CraigBladow/Heathkit-H8-Enclosure/openscad/H8_side_panels.scad

// Heathkit H8 Computer Enclosure - Side Panels
// Copyright 2024 Craig Bladow
// Released under MIT license:
//          https://github.com/CraigBladow/Heathkit-H8-Enclosure/blob/main/LICENSE

include <H8_parameters.scad>

//Panel Modules
module RoundedEdge(thickness, radius)
{
    rotate([0,0,0])cylinder(h=thickness, r = radius, center = true);
}

module Ledge(L,H,R)
{
    hull()
    {
        translate([0,L/2-R/2,0])cylinder(H,R,R,center=true);
        translate([0,-(L/2-R/2),0])cylinder(H,R,R,center=true);
    }
}

module LidLedge(side)
{
    color("lime")translate([PanelHeight/2-LedgeHeight/2-LedgeRecess,-LedgeOffset,side*(PanelThickness/2+LedgeWidth/2)])rotate([0,0,0]) Ledge(LedgeLength,LedgeWidth,LedgeHeight/2);
}

module FrontPanelLedge(side)
{
    
    color("lime")translate([FP_LedgeOffsetVertical,FP_LedgeOffsetHorizontal,side*(PanelThickness/2+FP_LedgeWidth/2)])
        rotate([0,0,FP_LedgeAngle]) 
            Ledge(FP_LedgeLength,FP_LedgeWidth,FP_LedgeHeight/2);
}

module FrontPanelBracketMount(side)
{
    
    color("lime")translate([FP_LedgeOffsetVertical,FP_LedgeOffsetHorizontal,side*(PanelThickness/2)])

    rotate([0,0,FP_LedgeAngle-90 ]) 
    {
        translate([-FPB_LengthLongShift,-FPB_LengthShortWidth/2+0.2,0])FrontPCB_Bracket();//0.2 is a magic tweak
    }
}

module FrontPanelBracketMountInsets(side)
{
    
    translate([FP_LedgeOffsetVertical,FP_LedgeOffsetHorizontal,side*(PanelThickness/2-Insert_6_32_hole_depth/2)])
        rotate([0,0,FP_LedgeAngle-90 ]) 
    {
             translate([-FPB_LengthLongShift-FPB_LengthLong/2 +(FPB_HoleDiameter*1.75)- FPB_MountShift,-FPB_LengthShortWidth/2+0.2,0])     translate([0,0,0]) rotate([0,0,180]) Insert_IUB_632_2(); 
                          translate([-(FPB_LengthLongShift-FPB_LengthLong/2 +(FPB_HoleDiameter*1.75)- FPB_MountShift)-FPB_UpperHoleShift,-FPB_LengthShortWidth/2+0.2,0])     translate([0,0,0]) rotate([0,0,180]) Insert_IUB_632_2(); 
    }
    
}

module OrigPanel()  // todo delete
{
    hull()
    {
        translate([PanelHeight/2-PanelCornerRadius,-PanelOverallLength/2+PanelCornerRadius,0])RoundedEdge(PanelThickness,PanelCornerRadius);  // upper rear corner
        translate([-PanelHeight/2+PanelCornerRadius,-PanelOverallLength/2+PanelCornerRadius,0])RoundedEdge(PanelThickness,PanelCornerRadius);  // lower rear corner

        
        translate([-PanelHeight/2+PanelCornerRadius+PanelFrontBottomRecessHeight,PanelOverallLength/2-PanelCornerRadius,0])RoundedEdge(PanelThickness,PanelCornerRadius);  // lower front corner (not bottom)
        translate([-PanelHeight/2+PanelCornerRadius,PanelOverallLength/2-PanelCornerRadius-PanelFrontBottomRecessLength,0])RoundedEdge(PanelThickness,PanelCornerRadius);  // bottom front corner (recessed)
        translate([PanelHeight/2-PanelCornerRadius,PanelTopLength-PanelOverallLength/2-PanelCornerRadius,0])RoundedEdge(PanelThickness,PanelCornerRadius);  // upper front corner

    }
}

module Panel()
{
    R = PanelCornerRadius;
    D = R * 2;
    PH = PanelHeight/2 - R;
    POL = PanelOverallLength/2 - R;
    linear_extrude(PanelThickness, center = true)
        offset(r = PanelCornerRadius)
            polygon([ [PH,-POL],
                      [-PH,-POL],        
                      [-PH,POL - PanelFrontBottomRecessLength],
                      [-PH+PanelFrontBottomRecessHeight,POL],
                      [PH,PanelTopLength-PanelOverallLength/2]]);   
}


module BackPanelBoltHoles()
{
    BoltClearanceY_Offset = 0;
    BoltClearanceX_Offset1 = BackPanelMountLength/2 -WasherRecessDiameterTopNo8;
    BoltClearanceX_Offset2 = -BoltClearanceX_Offset1;
    BoltClearanceZ_Offset = -(BackPanelThickness+BaseMountThickness+0)/2+WasherEmbossDepth;

    color("Magenta")translate([BoltClearanceX_Offset1,BoltClearanceY_Offset,BoltClearanceZ_Offset])rotate([180,0,0])BoltWasherHoleNo8();
    color("Magenta")translate([BoltClearanceX_Offset2,BoltClearanceY_Offset,BoltClearanceZ_Offset])rotate([180,0,0])BoltWasherHoleNo8();
}

module BackPanelRails()
{ 
    difference(){
       // Back panel mounting rails

        translate([-BackPanelRailsOffset,-PanelOverallLength/2+BasePlateHeight/2+BackPanelRecess,PanelThickness/2+BaseMountLength/2])rotate([90,0,0])
       difference(){ 
            PanelMount(BackPanelMountLength);
            BackPanelBoltHoles();
        }
       // remove excess fillet on bottom    
       translate([0,-PanelOverallLength/2-PanelThickness*2,0])cube([PanelHeight,PanelThickness*4,PanelThickness*4],center=true);
    }

}

BasePlateMountingRailsOffset = -(PanelOverallLength-BaseMountWidth)/2 +(BackPanelRecess+BackSupportThickness);
//echo(BasePlateMountingRailsOffset = BasePlateMountingRailsOffset);
   
module BasePlateMountingRailBoltHoles()
{
    BoltClearanceX_Offset = -PanelHeight/2+BasePlateRecess+BasePlateHeight+BaseMountThickness/2-WasherEmbossDepth;
    BoltClearanceY_Offset1 = -WasherRecessDiameterTopNo8;
    BoltClearanceY_Offset2 = -BoltClearanceY_Offset1;
    BoltClearanceY_Offset3 = BaseMountWidth/2-WasherRecessDiameterTopNo8 + BasePlateMountingRailsOffset;
    BoltClearanceY_Offset4 = -BaseMountWidth/2 + WasherRecessDiameterTopNo8 + BasePlateMountingRailsOffset;//-BoltClearanceY_Offset3;
    
    color("Magenta")translate([BoltClearanceX_Offset,BoltClearanceY_Offset1,PanelThickness/2+BaseMountLength/2])rotate([0,90,0])BoltWasherHoleNo8();
    color("Magenta")translate([BoltClearanceX_Offset,BoltClearanceY_Offset2,PanelThickness/2+BaseMountLength/2])rotate([0,90,0])BoltWasherHoleNo8();
    color("Magenta")translate([BoltClearanceX_Offset,BoltClearanceY_Offset3,PanelThickness/2+BaseMountLength/2])rotate([0,90,0])BoltWasherHoleNo8();
    color("Magenta")translate([BoltClearanceX_Offset,BoltClearanceY_Offset4,PanelThickness/2+BaseMountLength/2])rotate([0,90,0])BoltWasherHoleNo8();    
    
}


module BasePlateMountingRails()
{

    difference(){   
            
        translate([-PanelHeight/2+BasePlateHeight/2+BasePlateRecess,BasePlateMountingRailsOffset,PanelThickness/2+BaseMountLength/2])rotate([90,0,90]) PanelMount(BaseMountWidth);

        // remove excess fillet on bottom    
        translate([-PanelHeight/2-PanelThickness*2,0,0])color("lime")cube([PanelThickness*4,PanelOverallLength,PanelThickness*4],center=true);
        
       BasePlateMountingRailBoltHoles(); 
                        
    }
}

module PCB_InsertMountPoints()
{
    Insert_IUB_632_2();
}


module LeftPanel()
{
    difference()
    {
        union()
        {
            Panel();
            LidLedge(left);
            FrontPanelLedge(left);
            BackPanelRails();
            BasePlateMountingRails();
            
        }
        SidePlaneMountingInsets();
        FrontPanelBracketMountInsets(left); 
        SidePlaneFrontPanelMountingInset();
        
    }
    
}


module PanelMount(PM_Width)
{
        translate([0,0,BasePlateHeight/2])BaseMount(PM_Width);
        translate([0,0,-BasePlateHeight/2])rotate([180,0,180])BaseMount(PM_Width);
}

module FrontLeftPanel()
{
    difference()
    {

        LeftPanel();
        
        // Leave a small gap so printed half panels fit together easily
        TheGap(PanelHeight * 2,Gap,PanelThickness * 8);
        
        // Remove other half of left panel
        translate([0,-PanelOverallLength/2,0]) cube([PanelHeight*2,PanelOverallLength,PanelThickness * 4],center=true);
        // Make Sockets for pins
        SidePinPlugSockets(PanelHeight);
    }
}


module TheGap(G_X,G_Y,G_T)
{
    union()
    {
        //cube([G_X,G_Y,G_T],center = true);
        BML = BaseMountLength+0.1;
        color("red") translate([0,0,-(-PanelThickness/2+ridge_h/2-BML/2)])cube([PanelHeight,2*ridge_w+Gap,ridge_h+BML],center=true);
    }
    
}


module RearLeftPanel()
{
    difference()
    {
        LeftPanel();
        TheGap(PanelHeight * 2,Gap,PanelThickness * 8);    
        // Remove other half of left panel
        translate([0,PanelOverallLength/2,0]) cube([PanelHeight*2,PanelOverallLength,PanelThickness * 4],center=true);
        // Make sockets for pins
        SidePinPlugSockets(PanelHeight);
    }
}

module RightPanel()
{
    rotate([180,0,0])mirror([0,1,0])LeftPanel();
}

module FrontRightPanel()
{
    rotate([180,0,0])mirror([0,1,0]) FrontLeftPanel();
}

module RearRightPanel()
{
    rotate([180,0,0])mirror([0,1,0]) RearLeftPanel();
}



module Insert_IUB_632_2()
{
    union()
    {
        translate([0,0,Insert_6_32_taper_length/2])cylinder(h = Insert_6_32_taper_length, r1 = Insert_6_32_bottom_dia/2,r2 = Insert_6_32_opening_dia/2, center = true); 
        translate([0,0,-(Insert_6_32_hole_depth - Insert_6_32_taper_length)/2])cylinder(h = (Insert_6_32_hole_depth - Insert_6_32_taper_length), r = Insert_6_32_bottom_dia/2, center = true);
        
    }
}


module SidePinSnap()
{
    rotate([90,0,0])difference()
    {
        union()
        {
            
            cube([SidePinLength, SidePinXY, SidePinXY], center=true);
            // Add snap bumps
            translate([(SidePinLength-SidePinSnapBumpLength)/2,0,(SidePinXY+SidePinSnapBumpHeight)/2]) cube([SidePinSnapBumpLength,SidePinXY,SidePinSnapBumpHeight],center=true);
            translate([(SidePinLength-SidePinSnapBumpLength)/2,0,-(SidePinXY+SidePinSnapBumpHeight)/2]) cube([SidePinSnapBumpLength,SidePinXY,SidePinSnapBumpHeight],center=true);
            translate([-(SidePinLength-SidePinSnapBumpLength)/2,0,(SidePinXY+SidePinSnapBumpHeight)/2]) cube([SidePinSnapBumpLength,SidePinXY,SidePinSnapBumpHeight],center=true);
            translate([-(SidePinLength-SidePinSnapBumpLength)/2,0,-(SidePinXY+SidePinSnapBumpHeight)/2]) cube([SidePinSnapBumpLength,SidePinXY,SidePinSnapBumpHeight],center=true);
            rotate([90,0,0])
            {
                translate([-SidePinXY,0,0])la_bosse();
                translate([SidePinXY,0,0])la_bosse();
            }
            
        }
        // create gap
        translate([(SidePinLength-SidePinSnapGapLength)/2,0,0])cube([SidePinSnapGapLength,SidePinXY,SidePinSnapGapWidth],center=true);
        translate([-(SidePinLength-SidePinSnapGapLength)/2,0,0])cube([SidePinSnapGapLength,SidePinXY,SidePinSnapGapWidth],center=true);
    }
}

module SidePin()
{
    cube([SidePinLength, SidePinXY, SidePinXY], center=true);
}

module SidePinSocket()
{
    cube([SidePinLength + SidePinTol, SidePinXY + SidePinTol, SidePinXY + SidePinTol], center=true);
}

module SidePinPlugSockets(SockePanelLength)
{
    for(i = [1 : PanelSocketsNumber])translate([(i*SockePanelLength/PanelSocketsNumber)-SockePanelLength/2-SockePanelLength/(2*PanelSocketsNumber),0,0])rotate([(i-0)*90+45,0,90])SidePinPlugSocket();
}


module la_bosse()  // a bump
{
        cube([0.8,SidePinXY + SidePinTol, SidePinXY],center=true);
}



module SidePinPlugSocket()
{

        union()
        {
            
            cube([SidePinLength+SidePinTol, SidePinXY+SidePinTol, SidePinXY+SidePinTol], center=true);
            // Add snap bumps
            translate([(SidePinLength-SidePinSnapBumpLength)/2,0,(SidePinXY+SidePinSnapBumpHeight)/2]) cube([SidePinSnapBumpLength+SidePinTol,SidePinXY+SidePinTol,SidePinSnapBumpHeight+SidePinTol],center=true);
            translate([(SidePinLength-SidePinSnapBumpLength)/2,0,-(SidePinXY+SidePinSnapBumpHeight)/2]) cube([SidePinSnapBumpLength+SidePinTol,SidePinXY+SidePinTol,SidePinSnapBumpHeight+SidePinTol],center=true);
            translate([-(SidePinLength-SidePinSnapBumpLength)/2,0,(SidePinXY+SidePinSnapBumpHeight)/2]) cube([SidePinSnapBumpLength+SidePinTol,SidePinXY+SidePinTol,SidePinSnapBumpHeight+SidePinTol],center=true);
            translate([-(SidePinLength-SidePinSnapBumpLength)/2,0,-(SidePinXY+SidePinSnapBumpHeight)/2]) cube([SidePinSnapBumpLength+SidePinTol,SidePinXY+SidePinTol,SidePinSnapBumpHeight+SidePinTol],center=true);
            // Add flare for pins

            hull()
            {
                rotate([0,45,0])cube([SidePinXY+SidePinTol,SidePinXY+SidePinTol,SidePinXY+SidePinTol],center=true);
                rotate([0,90,0])cube([SidePinXY+SidePinTol,SidePinXY+SidePinTol,SidePinXY+SidePinTol],center=true);
            }
            
            
            rotate([90,0,0])
            {
                            translate([(SidePinLength-SidePinSnapBumpLength)/2,0,(SidePinXY+SidePinSnapBumpHeight)/2]) cube([SidePinSnapBumpLength+SidePinTol,SidePinXY+SidePinTol,SidePinSnapBumpHeight+SidePinTol],center=true);
            translate([(SidePinLength-SidePinSnapBumpLength)/2,0,-(SidePinXY+SidePinSnapBumpHeight)/2]) cube([SidePinSnapBumpLength+SidePinTol,SidePinXY+SidePinTol,SidePinSnapBumpHeight+SidePinTol],center=true);
            translate([-(SidePinLength-SidePinSnapBumpLength)/2,0,(SidePinXY+SidePinSnapBumpHeight)/2]) cube([SidePinSnapBumpLength+SidePinTol,SidePinXY+SidePinTol,SidePinSnapBumpHeight+SidePinTol],center=true);
            translate([-(SidePinLength-SidePinSnapBumpLength)/2,0,-(SidePinXY+SidePinSnapBumpHeight)/2]) cube([SidePinSnapBumpLength+SidePinTol,SidePinXY+SidePinTol,SidePinSnapBumpHeight+SidePinTol],center=true);
            
            }
        }

}

// Rail for the side panel to attach it to the Base Plate
module BaseMount(BM_Width)
{
    difference()
    {
        translate([0,0,BaseMountFilletRadius*2+BaseMountThickness/2])cube([BM_Width,BaseMountLength, BaseMountFilletRadius*4 + BaseMountThickness],center = true);
        
       translate([0,-BaseMountFilletRadius/2,BaseMountFilletRadius+BaseMountThickness/2])hull()
        {
            translate([0,0,BaseMountFilletRadius*2+BaseMountThickness])cube([BM_Width,BaseMountFilletRadius*2,BaseMountFilletRadius*2],center = true);
            translate([0,BaseMountLength-BaseMountFilletRadius/2,BaseMountFilletRadius*2+BaseMountThickness])cube([BM_Width,BaseMountFilletRadius*2,BaseMountFilletRadius*2],center = true);
            translate([0,BaseMountLength-BaseMountFilletRadius/2,0])cube([BM_Width,BaseMountFilletRadius*2,BaseMountFilletRadius*2],center = true);
    
            translate([0,0,0])rotate([0,90,0])cylinder(h = BM_Width, r = BaseMountFilletRadius,center = true);
        }
    }
    
}


module TestSocket()
{
    difference()
    {
        cube([SidePinLength/2,2*SidePinXY,2*SidePinXY],center=true);
        rotate([45,0,0])SidePinSocket();
    }
}

module TestPlugSocket()
{
    difference()
    {
        cube([SidePinLength,2*SidePinXY,PanelThickness],center=true);
        //translate([SidePinLength/2+SidePinTol,0,0])
        translate([-SidePinLength/2,0,0])rotate([45,0,0])SidePinPlugSocket();
    }
}


// test for inner and mounting tab dimensions
module TestFrontLeftSidePanelSubSection()
{
    $fn = 128;
    difference()
    {
        
        FrontLeftPanel();
        //translate([0,BaseMountWidth/2,(PanelThickness-Insert_6_32_hole_depth)/2])Insert_IUB_632_2();
        color("lime")translate([0,PanelOverallLength/2+mm(1.0),0]) cube([PanelHeight*2,PanelOverallLength,PanelThickness * 4],center=true);
    }

}



module TestRearLeftSidePanelSubSection()
{
    $fn = 128;
    difference()
    {
        
        RearLeftPanel(); //translate([0,BaseMountWidth/2,(PanelThickness-Insert_6_32_hole_depth)/2])Insert_IUB_632_2();
        color("lime")translate([0,-PanelOverallLength/2-mm(1.0),0]) cube([PanelHeight*2,PanelOverallLength,PanelThickness * 4],center=true);
    }

}


module FrontPCB_BracketSlot()
{
    hull()
    {
        translate([FPB_HoleDiameter*1.5,0,0])cylinder(h=FPB_Thickness * 2, r = FPB_HoleDiameter/2, center=true);
        translate([-FPB_HoleDiameter*1.5,0,0])cylinder(h=FPB_Thickness * 2, r = FPB_HoleDiameter/2, center=true);
    }
    
}

// The short piece attaches to the front panel PCB
module FrontPCB_Bracket()
{
    union()
    {
       difference()
        {
            color( "magenta" ) translate([0,0,FPB_Thickness/2]) cube([FPB_LengthLong,FPB_LengthLongWidth,FPB_Thickness],center=true);
                        translate([FPB_LengthLongHoleSpacing/2,0,0]) FrontPCB_BracketSlot();//cylinder(h=FPB_Thickness * 2, r = FPB_HoleDiameter/2, center=true);
            translate([-FPB_LengthLongHoleSpacing/2,0,0]) FrontPCB_BracketSlot();//cylinder(h=FPB_Thickness * 2, r = FPB_HoleDiameter/2, center=true);
        }
            translate([0,-FPB_LengthLongWidth/2-FPB_Thickness/2,FPB_LengthShortWidth/2]) rotate([90,0,0]) difference()
        {
            cube([FPB_LengthShort,FPB_LengthShortWidth,FPB_Thickness],center=true);
            translate([FPB_HoleSpacing/2,FPB_HoleOffsetShort,0]) cylinder(h=FPB_Thickness * 2, r = FPB_HoleDiameter/2, center=true);
            translate([-FPB_HoleSpacing/2,FPB_HoleOffsetShort,0]) cylinder(h=FPB_Thickness * 2, r = FPB_HoleDiameter/2, center=true);
        }
        
    }
}





/*
module BoltWasherHoleNo8()
{
    union()
    {
        translate([0,0,-BoltLength3_4/2])cylinder(h = BoltLength3_4, r = BoltHoleDiameterNo8/2, center=true);
        translate([0,0,WasherRecessHeightNo8/2]) cylinder(h = WasherRecessHeightNo8, r1 = WasherRecessDiameterBottomNo8/2, r2 = WasherRecessDiameterTopNo8/2, center = true);
        translate([0,0,-BasePlateHeight-BaseMountThickness]) rotate([0,180,0])cylinder(h = WasherRecessHeightNo8, r1 = WasherRecessDiameterBottomNo8/2, r2 = WasherRecessDiameterTopNo8/2, center = true);
    }
    
} */

// No. 8 flat head bolt head dimensions
FlatHeadBolt8TopDia = mm(5/16);
FlatHeadBolt8BotDia = BoltHoleDiameterNo8;
FlatHeadBolt8Height = mm(0.125);
OldFlatHeadRecess = FlatHeadBolt8Height/2-2.2;
// move below to H8_Parameters
CardAssemblyHeightAboveBasePlate = mm(1/8);
FlatHeadRecess = FlatHeadBolt8Height/2-2.4;
//echo(OldFlatHeadRecess = OldFlatHeadRecess);
//echo(FlatHeadRecess = FlatHeadRecess);
//echo(BaseMountThickness = BaseMountThickness/2);

module BoltWasherHoleNo8()   // Flathead version
{
    union()
    {
        color("lime") translate([0,0,-BoltLength3_4/2])cylinder(h = BoltLength3_4, r = BoltHoleDiameterNo8/2, center=true);
        
        //color("orange") translate([0,0,WasherRecessHeightNo8/2]) cylinder(h = WasherRecessHeightNo8, r1 = WasherRecessDiameterBottomNo8/2, r2 = WasherRecessDiameterTopNo8/2, center = true);
        
        //translate([0,0,FlatHeadBolt8Height/2-3])
        translate([0,0,FlatHeadBolt8Height/2.8-mm(.1)])
       {
            union()
            {
               color("orange") cylinder(h = FlatHeadBolt8Height, r1 = FlatHeadBolt8BotDia/2, r2 = FlatHeadBolt8TopDia/2, center = true);
                color("blue") translate([0,0,FlatHeadBolt8Height]) cylinder(r = FlatHeadBolt8TopDia/2 +0.1 , h = FlatHeadBolt8Height,center=true);
            }
        }
        
        color("magenta")translate([0,0,-BasePlateHeight-BaseMountThickness]) rotate([0,180,0])cylinder(h = WasherRecessHeightNo8, r1 = WasherRecessDiameterBottomNo8/2, r2 = WasherRecessDiameterTopNo8/2, center = true);
    }
    
}

module SidePlaneMountingInsets()
{
    color("red")translate([0,-BasePlateLength/2,PanelThickness/2 - Insert_6_32_hole_depth/2 - .06])rotate([0,90,0])
        for(i = SP_MountLocations)
        {
            translate(i) rotate([0,90,180]) Insert_IUB_632_2();//cylinder(h=10,r = 2, center = true);
        }
}

module SidePlaneFrontPanelMountingInset()
{
    // todo delete commented out code
    //color("red")translate([0,0,PanelThickness/2 - Insert_6_32_hole_depth/2 - .06])rotate([0,90,0])
        //for(i = FP_MountLocations)
        //{
            //color("red")translate([FP_X,FP_Y,0]) rotate([0,0,0]) cylinder(h=20,r = Insert_6_32_opening_dia/2, center = true); //Insert_IUB_632_2();
        //}

        color("blue")translate([FP_LedgeOffsetVertical,FP_LedgeOffsetHorizontal,(PanelThickness/2-Insert_6_32_hole_depth/2)])
        rotate([0,0,FP_LedgeAngle-90 ]) 
    {       //first line not reachable for assembly
            //translate([-FPB_LengthLongShift-FPB_LengthLong/2 +(FPB_HoleDiameter*1.75)-FP_Mount_Offset,-FPB_LengthShortWidth/2+0.2,0]) translate([0,0,0]) rotate([0,0,180]) Insert_IUB_632_2(); 
            translate([-(FPB_LengthLongShift-FPB_LengthLong/2 +(FPB_HoleDiameter*1.75))+FP_Mount_Offset,-FPB_LengthShortWidth/2+0.2,0]) translate([0,0,0]) rotate([0,0,180]) Insert_IUB_632_2(); 
    }
    
}

echo (Insert_6_32_hole_depth = Insert_6_32_hole_depth/2);

//translate([-PanelThickness/2-BasePlateWidth+PCB_Thickness/2+SP_PCB_StandOffHeight,-BasePlateLength/2,-(PanelHeight/2 - SidePlanePCBHeight/2)+(BasePlateHeight+BasePlateRecess)+SP_PCB_HeightFromCaseBottom]) 
//color("lime")translate([0,-BasePlateLength/2,PanelThickness/2])rotate([0,90,0])SidePlaneMountingInsets();

//BackPanelRails();
//BasePlateMountingRails();
//FrontLeftPanel();

//FlatHeadBoltWasherHoleNo8();
//echo (FlatHeadBolt8Height = FlatHeadBolt8Height);

//BasePlateMountingRailBoltHoles();

module TestSideChunk()
{
    difference()
    {
        TestFrontLeftSidePanelSubSection();
        translate([20,0,0])cube([140,60,20],center=true);
    }
}



module SidePlaneMountingPegs()
{
    color("red")translate([0,-BasePlateLength/2,PanelThickness/2 - Insert_6_32_hole_depth/2 - .06])rotate([0,90,0])
        for(i = SP_MountLocations)
        {
            translate(i) rotate([0,90,180]) cylinder(h=15,r = 2, center = true); //Insert_IUB_632_2();
        }
}


module TestPegsRightPanel()
{
    rotate([180,0,0])mirror([0,1,0])
    {
        difference()
        {
            union()
            {
                Panel();
                //LidLedge(left);
                //FrontPanelLedge(left);
                //BackPanelRails();
                //BasePlateMountingRails();
                SidePlaneMountingPegs();

                //translate ([0,200,0]) rotate([0,0,FP_LedgeAngle])  color("red") translate([0,0,0])cube([150,600,30],center=true);
                //rotate([0,0,FP_LedgeAngle])  color("red") translate([0,0,0])cube([150,600,30],center=true);
                
            }
            color("red") translate([0,0,-10])cube([400,600,20],center=true);
            color("red") translate([95,0,0])cube([50,600,30],center=true);
            color("red") translate([-95,0,0])cube([50,600,30],center=true);
            translate ([0,-235,0]) rotate([0,0,FP_LedgeAngle])  color("red") translate([0,0,0])cube([150,600,30],center=true);
            translate ([0,200,0]) rotate([0,0,FP_LedgeAngle])  color("red") translate([0,0,0])cube([150,600,30],center=true);
        }
        
    }
}

module RearPegTriangle()
{
  difference()
  {
    TestPegsRightPanel();
      translate ([0,75,0]) rotate([0,0,177-FP_LedgeAngle])  color("red") translate([0,0,0])cube([250,800,30],center=true);
      translate([20,-110,0])color("red") cylinder(h=20,r=35,center=true);
      translate([63,-110,0])color("red") cylinder(h=20,r=4,center=true);
  }
  //translate ([0,75,0]) rotate([0,0,177-FP_LedgeAngle])  color("red") translate([0,0,0])cube([250,800,30],center=true);
  //translate([20,-110,0])color("red") cylinder(h=20,r=35,center=true);
  
}

module MiddlePegTriangle()
{
  difference()
  {
    TestPegsRightPanel();
            translate ([0,-230,0]) rotate([0,0,175-FP_LedgeAngle])  color("red") translate([0,0,0])cube([250,800,30],center=true);
  translate ([0,140,0]) rotate([0,0,FP_LedgeAngle])  color("red") translate([0,0,0])cube([250,800,30],center=true);
translate([-18,-50,0])color("red") cylinder(h=20,r=35,center=true);
  translate([40,-52,0])color("red") cylinder(h=20,r=4,center=true);
  }

  

}




module FrontPegTriangle()
{
  difference()
  {
    TestPegsRightPanel();
    translate ([0,-110,0]) rotate([0,0,175-FP_LedgeAngle])  color("red") translate([0,0,0])cube([250,800,30],center=true);
  //translate ([0,140,0]) rotate([0,0,FP_LedgeAngle])  color("red") translate([0,0,0])cube([250,800,30],center=true);
translate([-18,70,0])color("red") cylinder(h=20,r=35,center=true);
translate([40,70,0])color("lime") cube([8,8,20],center=true);//cylinder(h=20,r=4,center=true);
  }
  
  

}


module FrontMiddlePegTriangle()
{
  difference()
  {
    TestPegsRightPanel();
    translate ([0,-180,0]) rotate([0,0,FP_LedgeAngle])  color("red") translate([0,0,0])cube([250,800,30],center=true);
  translate ([0,190,0]) rotate([0,0,175 - FP_LedgeAngle])  color("red") translate([0,0,0])cube([250,800,30],center=true);
translate([15,5,0])color("red") cylinder(h=20,r=35,center=true);
translate([60,-0,0])color("lime") cylinder(h=20,r=4,center=true);
      translate([60,16,0])color("lime") cylinder(h=20,r=4,center=true);
  }
  
  

}

//TestSideChunk();

/*
difference()
{
    cube([14,14,mm(0.1)],center=true);
    translate([0,0,FlatHeadBolt8Height/2.8-mm(.02)])BoltWasherHoleNo8();
    
}
*/

//translate([0,0,+FlatHeadBolt8Height/2.8-mm(.02)])BoltWasherHoleNo8();
//$fn = 128;
//TestPegsRightPanel();

//RearPegTriangle();
//MiddlePegTriangle();
//FrontMiddlePegTriangle();
//FrontPegTriangle();











 
